movasim/eSense-Rubino/images/eSense-Rubino-v1.1.1-1.jpg

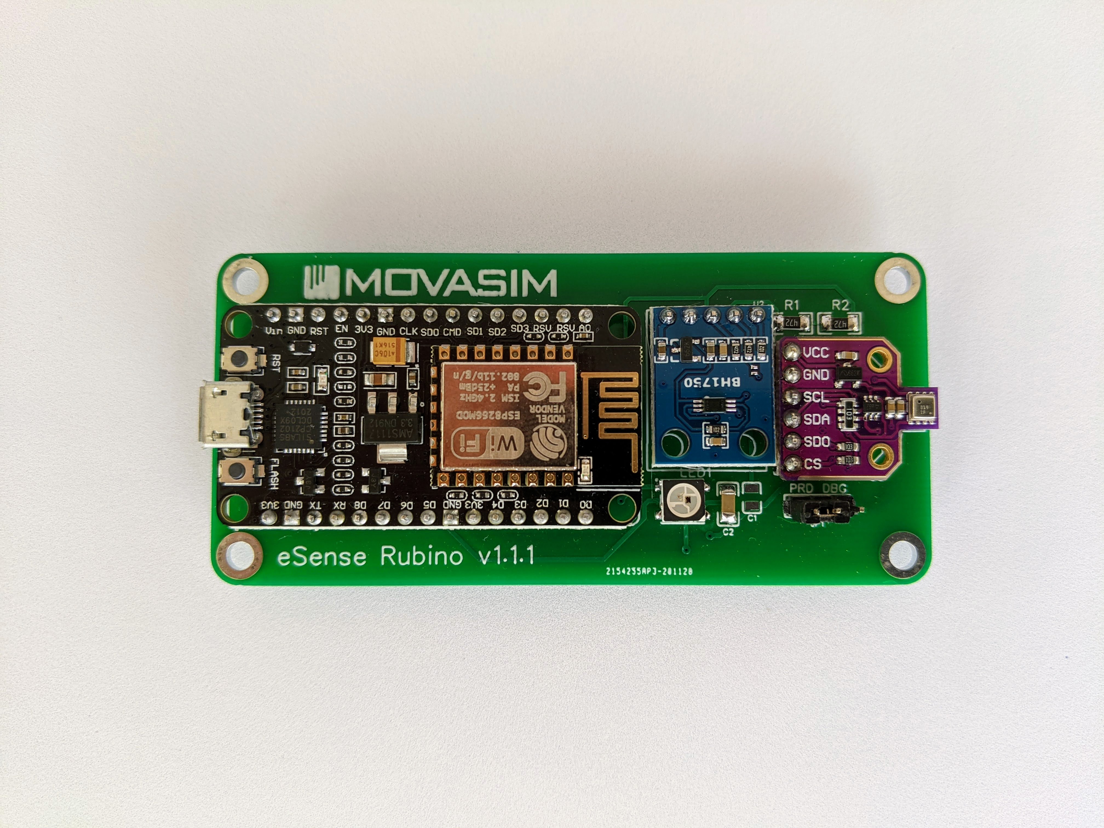
images/eSense-Rubino-v1.1.1-1.jpg
